Letstech/Audio-Project/documentation/Fritzing Steps/1_bb.png

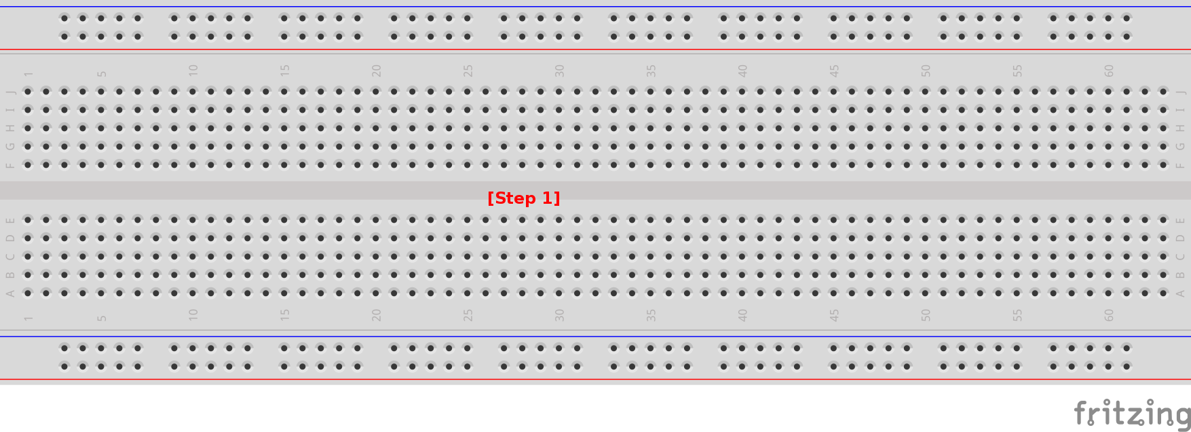
documentation/Fritzing Steps/1_bb.png
