Letstech/Audio-Project/documentation/Fritzing Steps/3_bb.png

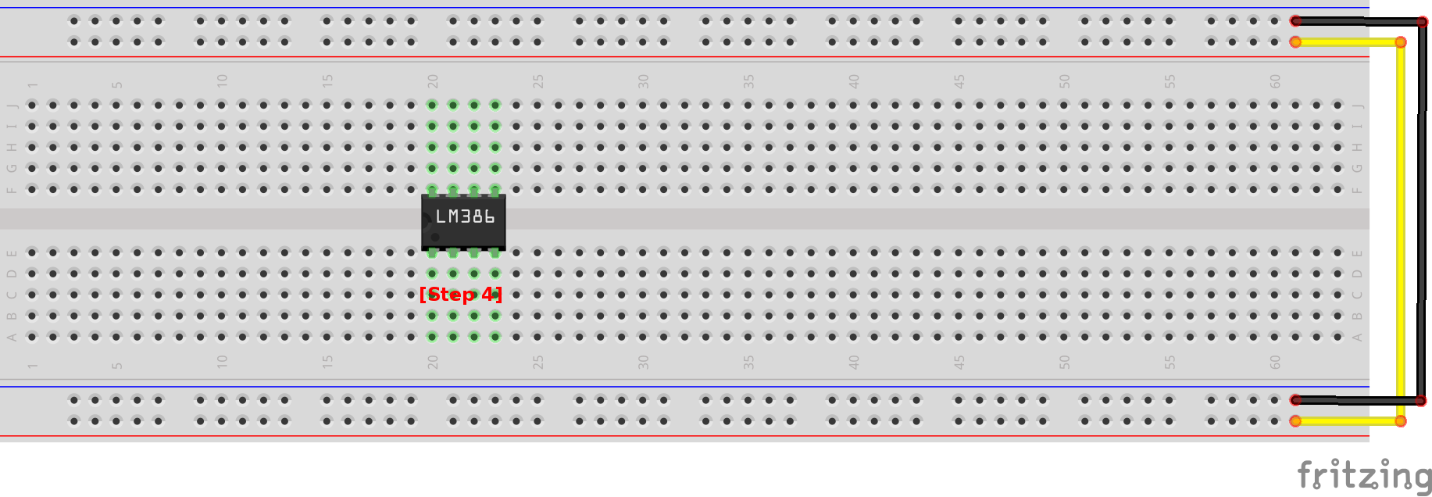
documentation/Fritzing Steps/3_bb.png
