Letstech/Audio-Project/documentation/Fritzing Steps/9_bb.png

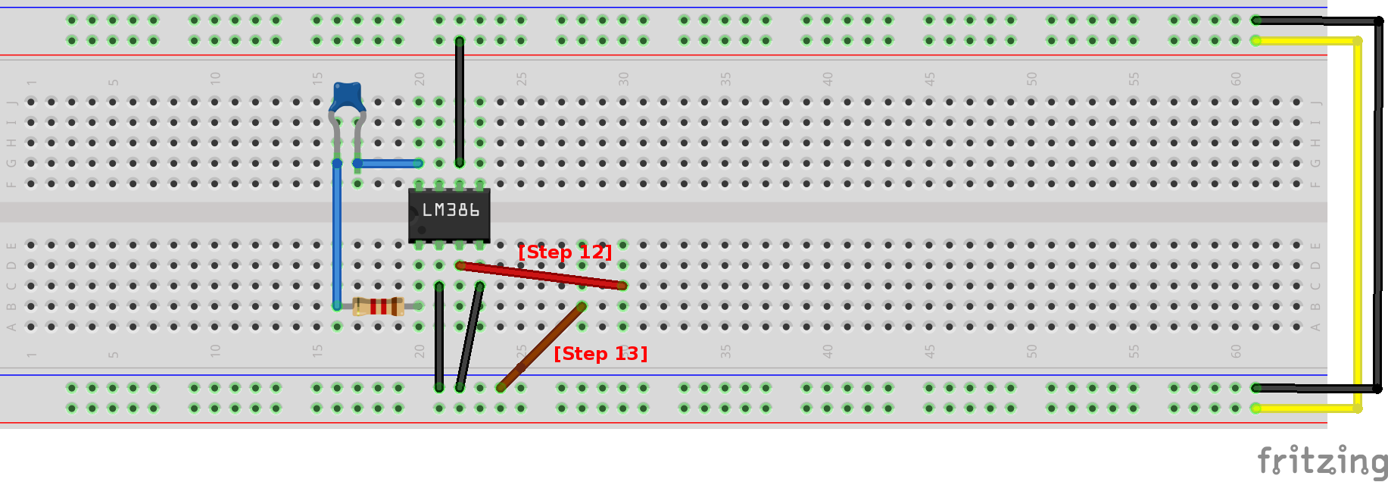
documentation/Fritzing Steps/9_bb.png
