Letstech/Audio-Project/documentation/Fritzing Steps/10_bb.png

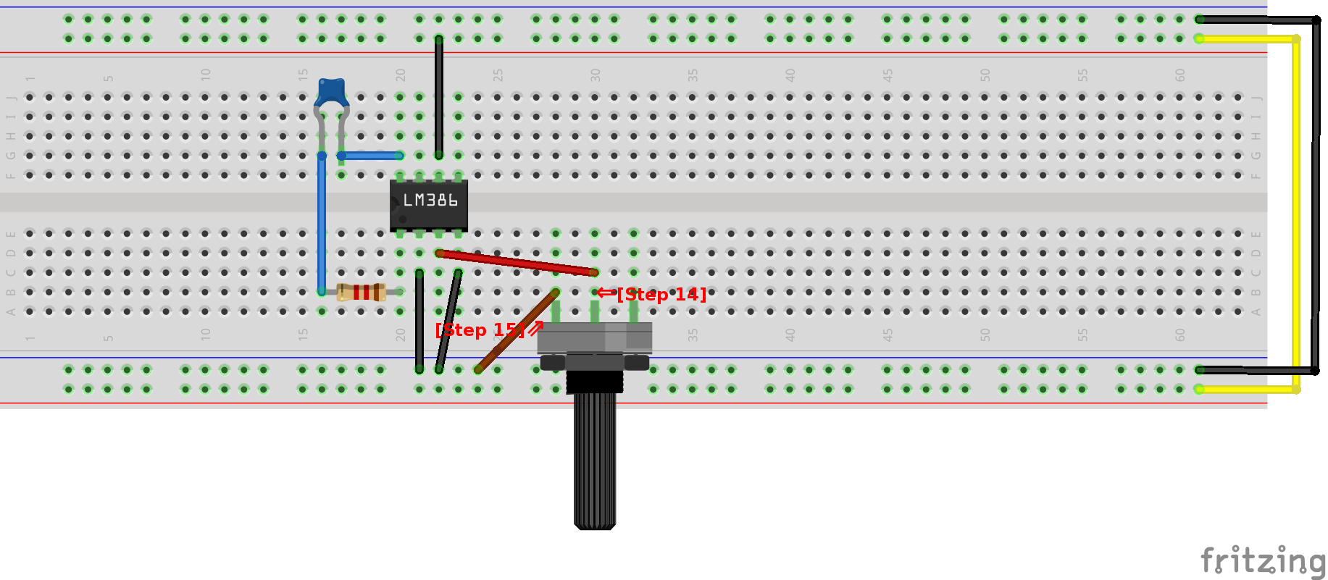
documentation/Fritzing Steps/10_bb.png
