Letstech/Audio-Project/documentation/Fritzing Steps/11_bb.png

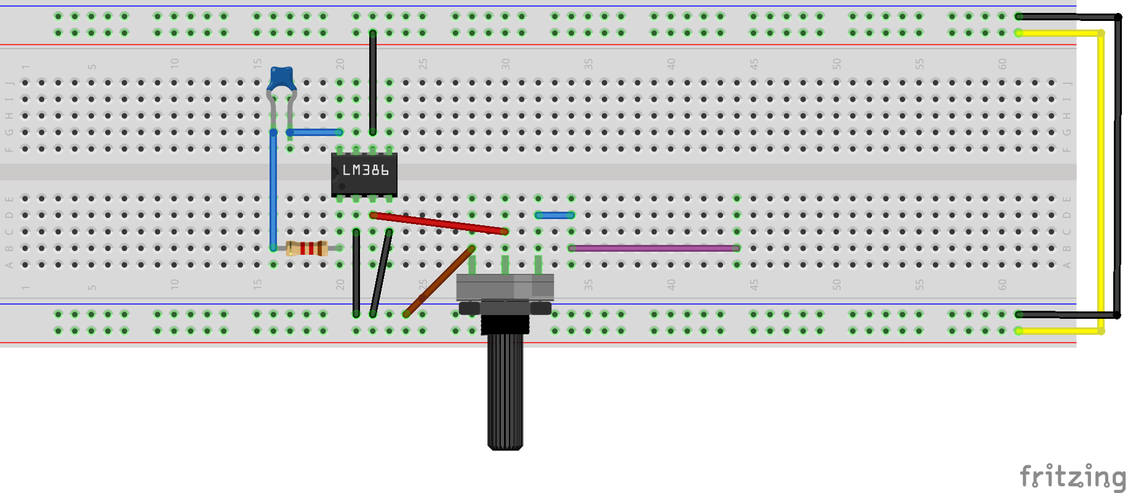
documentation/Fritzing Steps/11_bb.png
