Letstech/Audio-Project/documentation/Fritzing Steps/15_bb.png

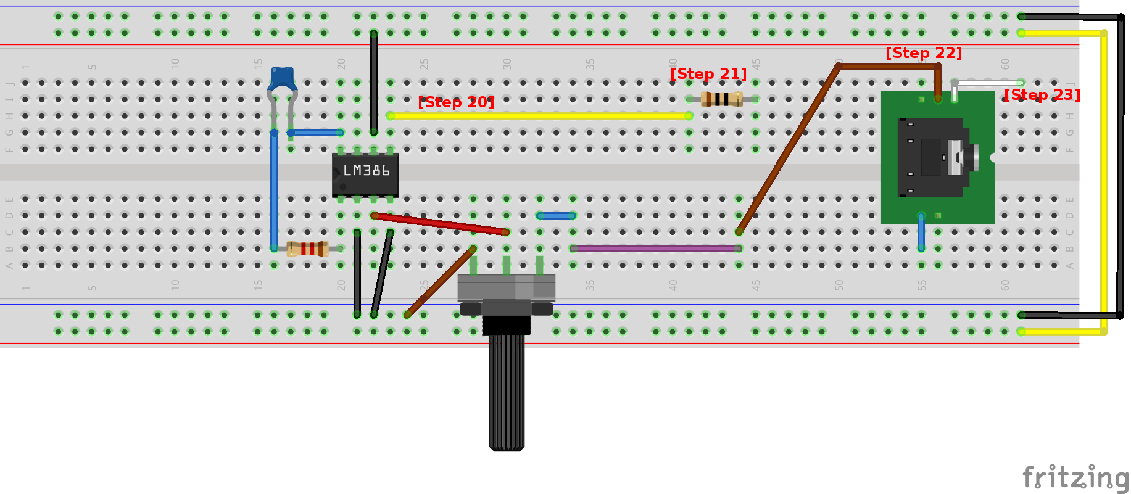
documentation/Fritzing Steps/15_bb.png
