Letstech/Audio-Project/documentation/Fritzing Steps/17_bb.png

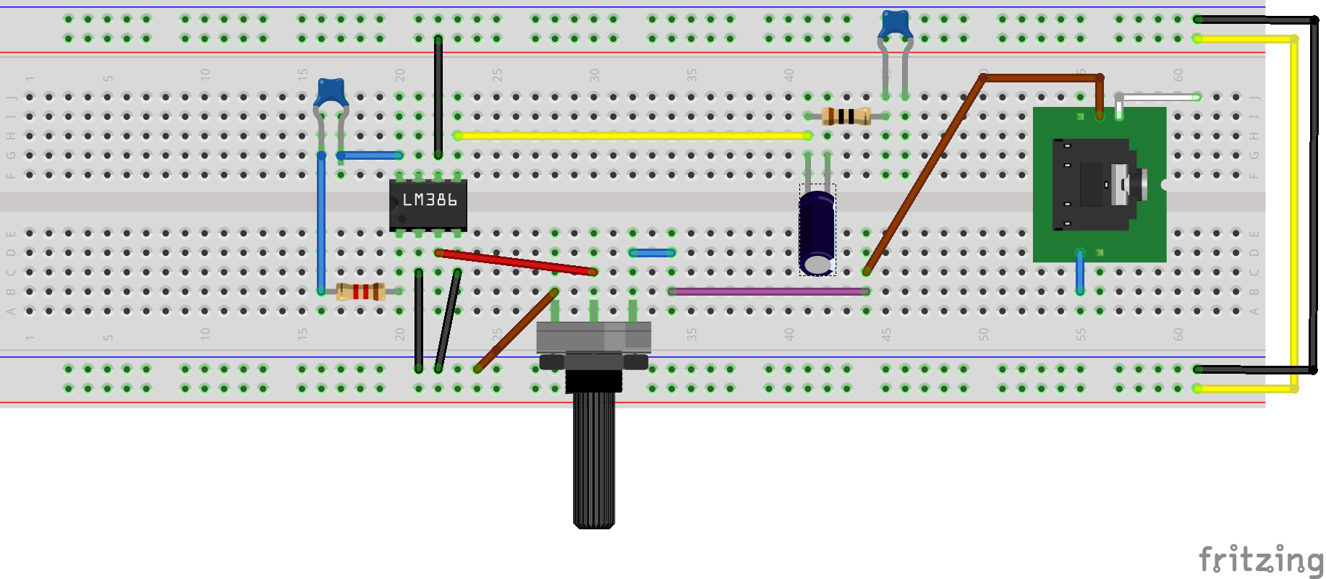
documentation/Fritzing Steps/17_bb.png
