Letstech/Audio-Project/documentation/Fritzing Steps/19_bb.png

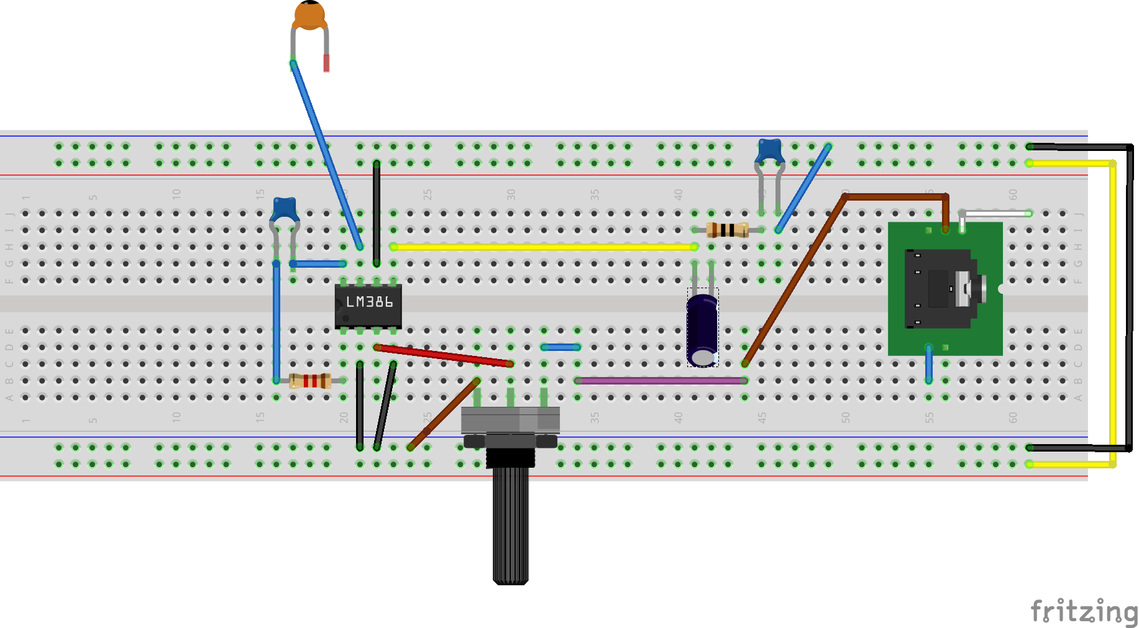
documentation/Fritzing Steps/19_bb.png
