Letstech/Audio-Project/documentation/Fritzing Steps/21_bb.png

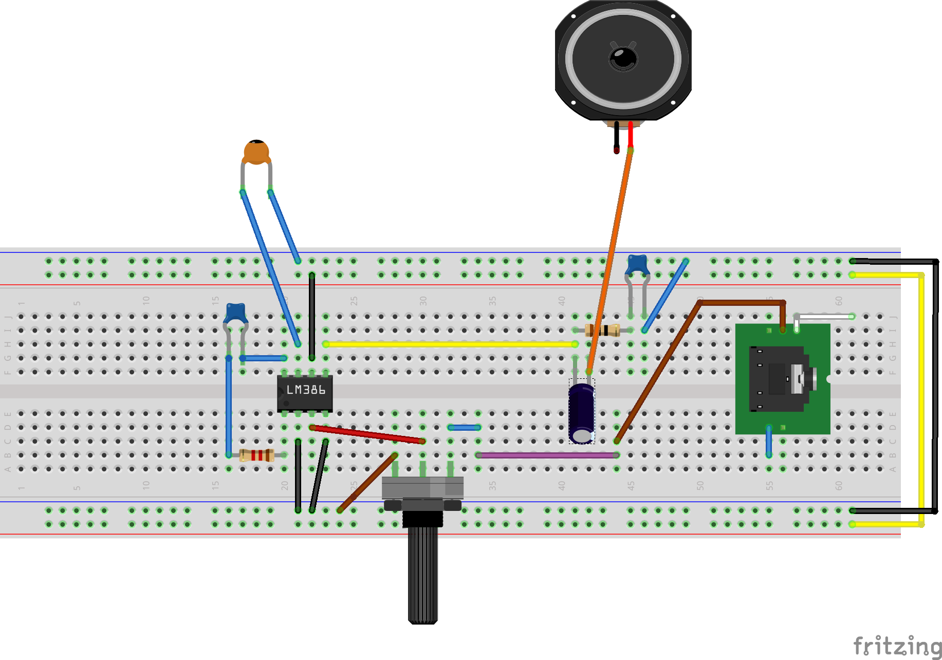
documentation/Fritzing Steps/21_bb.png
