Letstech/Audio-Project/documentation/Fritzing Steps/23_bb.png

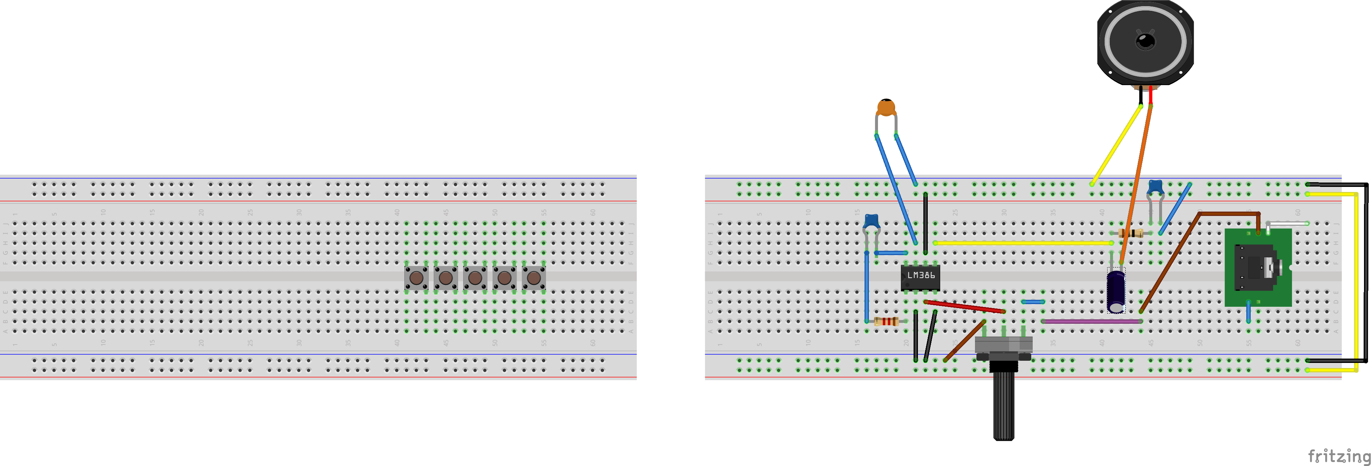
documentation/Fritzing Steps/23_bb.png
