Letstech/Audio-Project/documentation/Fritzing Steps/28_bb.png

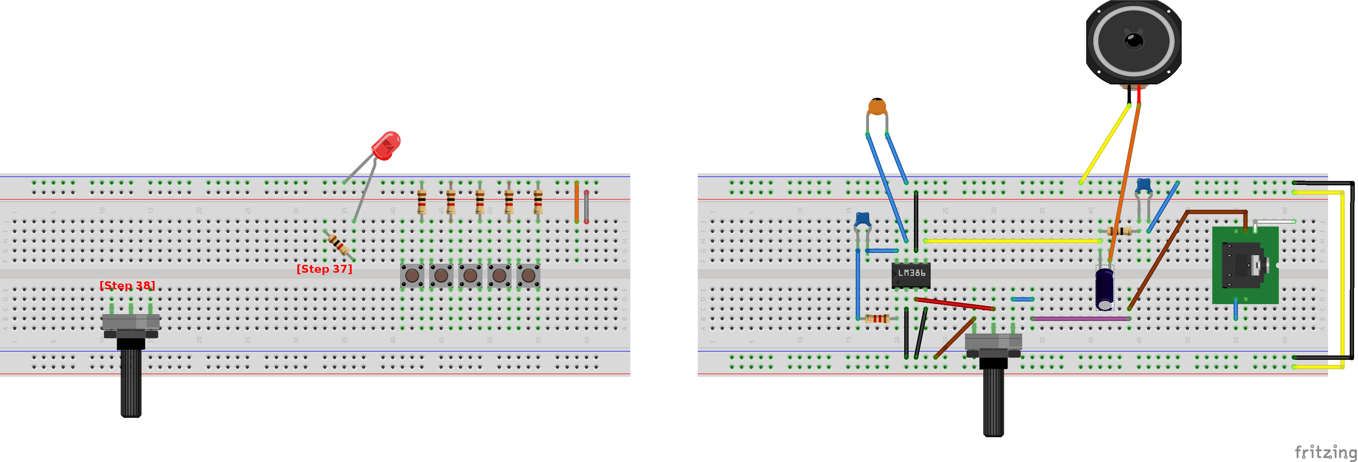
documentation/Fritzing Steps/28_bb.png
