Letstech/Audio-Project/documentation/Fritzing Steps/37_bb.png

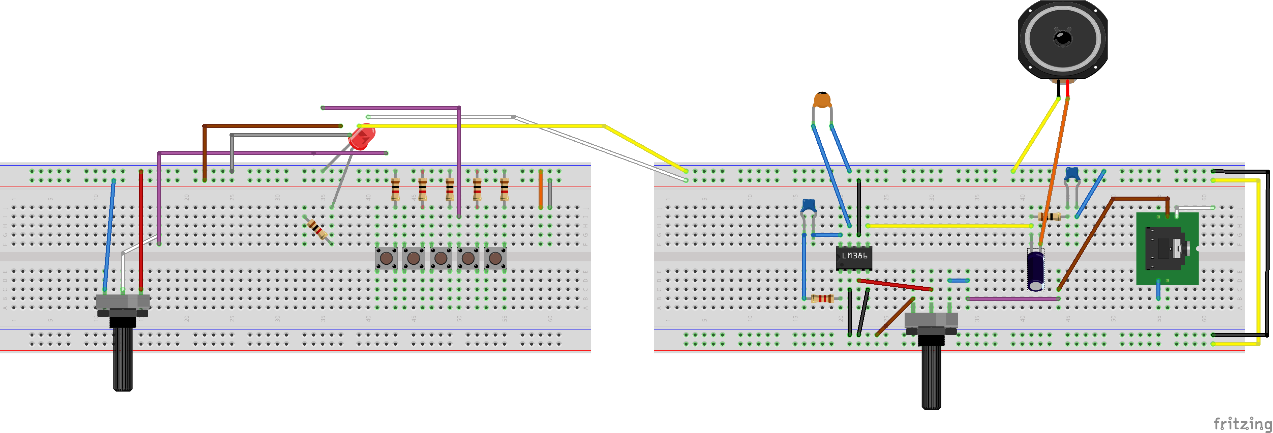
documentation/Fritzing Steps/37_bb.png
