Letstech/Audio-Project/documentation/Fritzing Steps/38_bb.png

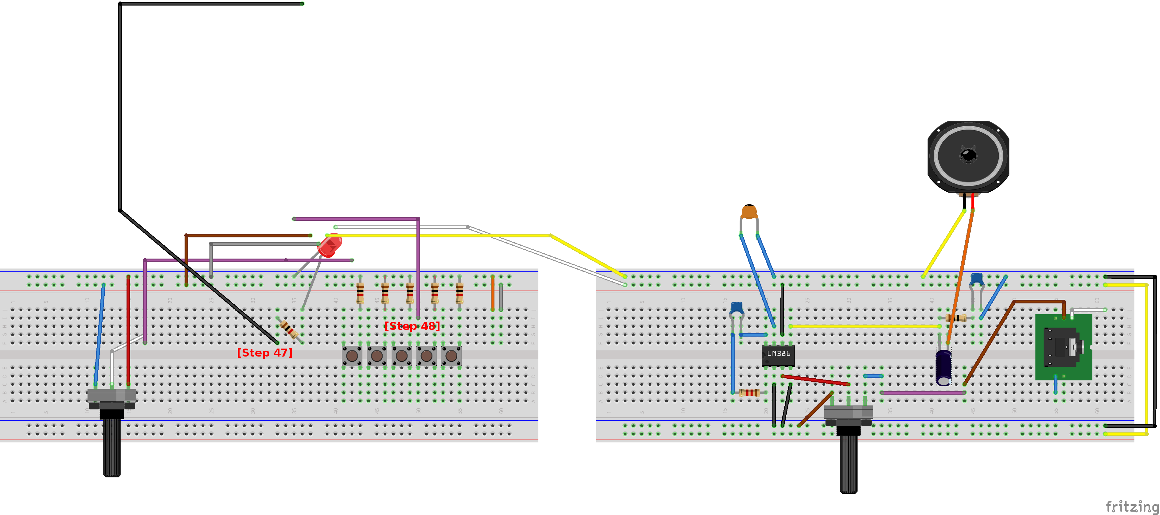
documentation/Fritzing Steps/38_bb.png
