Letstech/Audio-Project/documentation/Fritzing Steps/40_bb.png

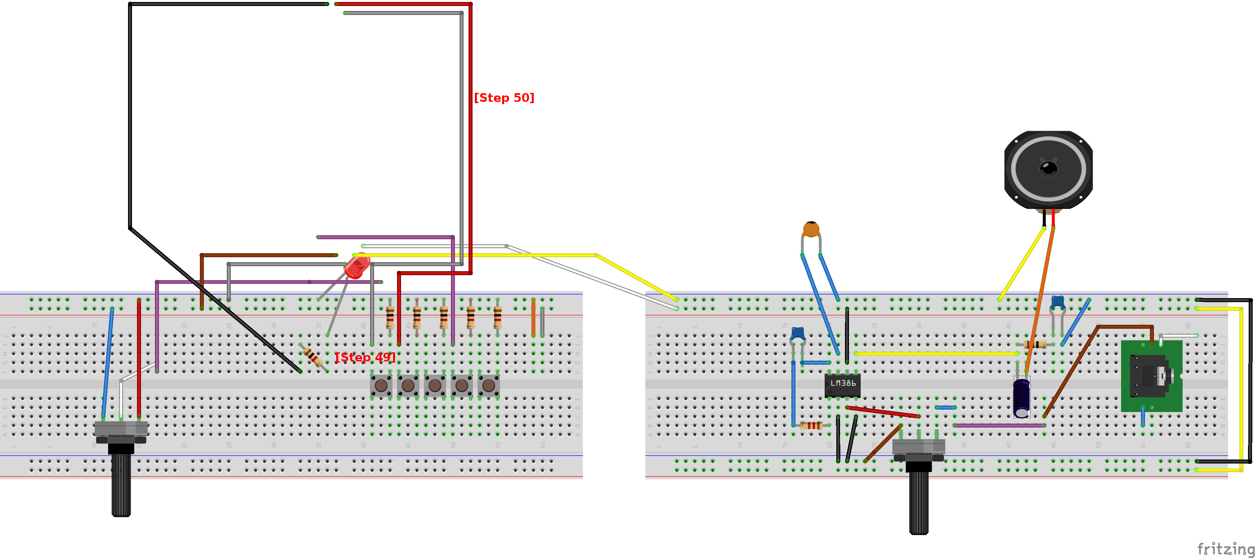
documentation/Fritzing Steps/40_bb.png
