Letstech/Audio-Project/documentation/Fritzing Steps/44_bb.png

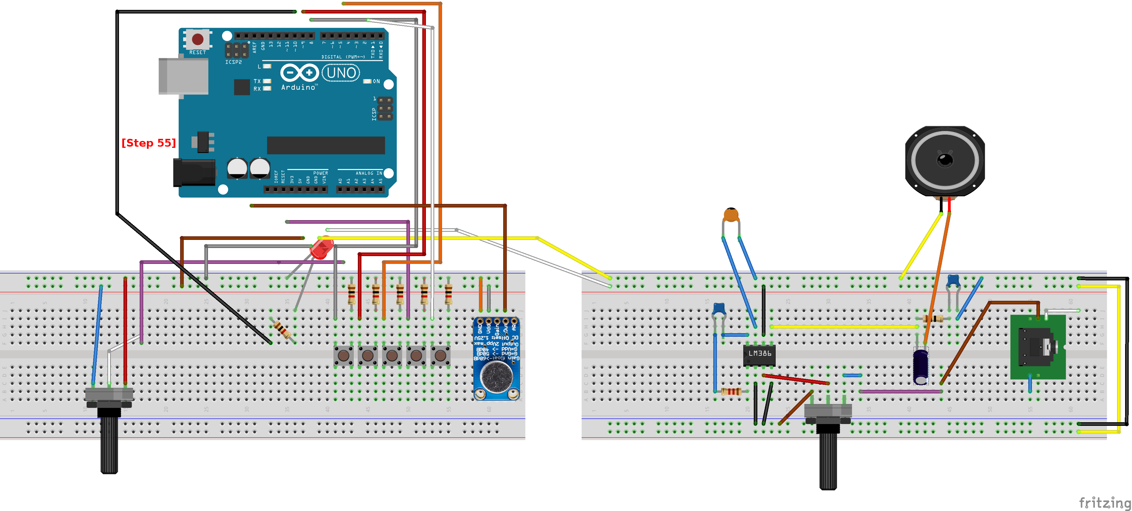
documentation/Fritzing Steps/44_bb.png
